IlorDash/HAQuDA/Data/Article/Photos/Assembly_slice.png

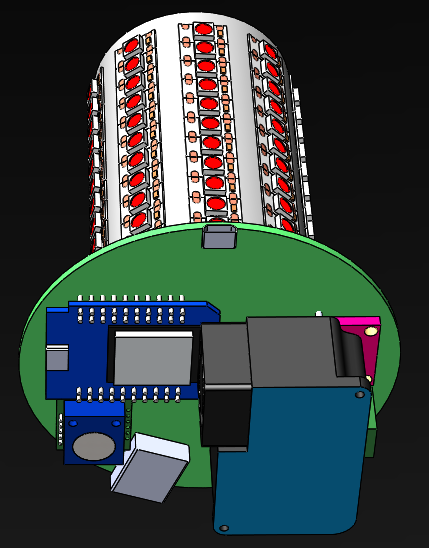
Data/Article/Photos/Assembly_slice.png
