IlorDash/HAQuDA/Data/Article/Photos/Assembly.png

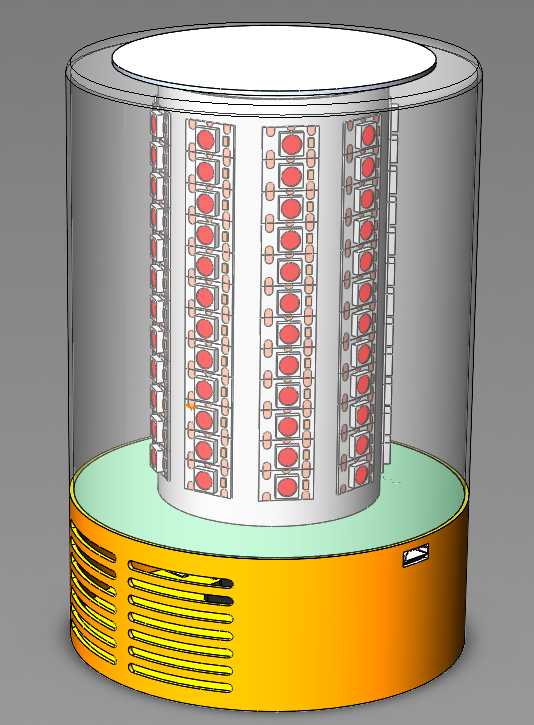
Data/Article/Photos/Assembly.png
