IlorDash/HAQuDA/Data/Article/Photos/AmbientOrb_1.jpg

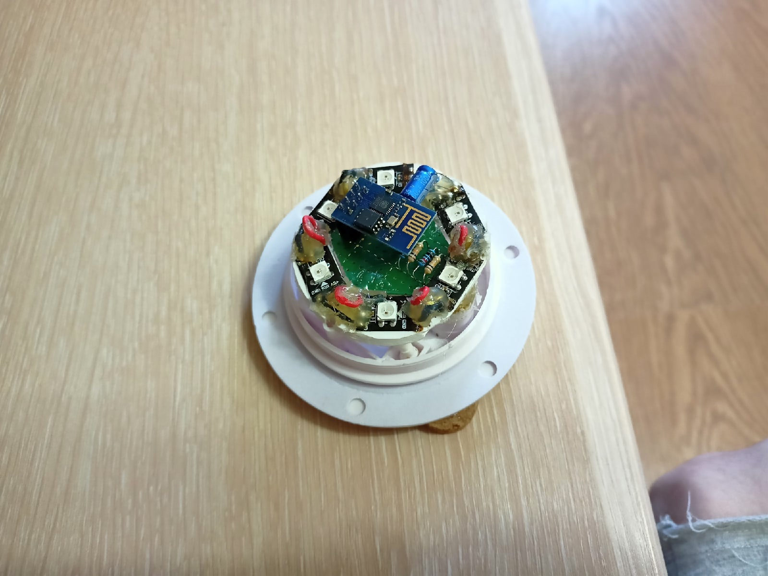
Data/Article/Photos/AmbientOrb_1.jpg
