IlorDash/HAQuDA/Data/Article/Photos/AmbientOrb_DHT_1.jpg

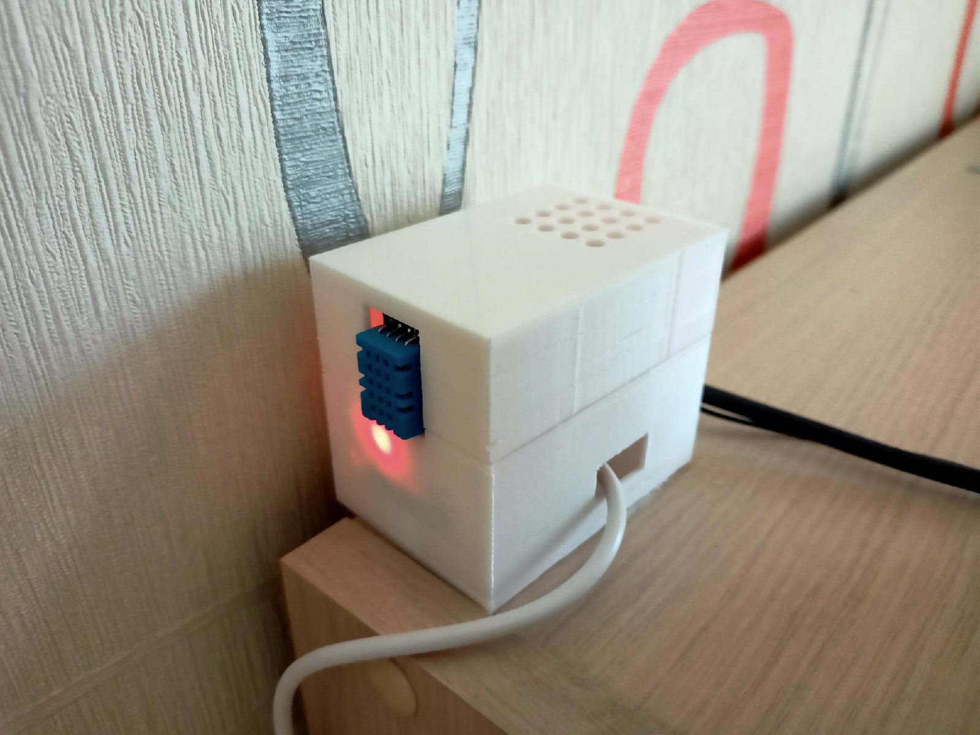
Data/Article/Photos/AmbientOrb_DHT_1.jpg
