IlorDash/HAQuDA/Data/Article/Photos/AmbientOrb_DHT_2.jpg

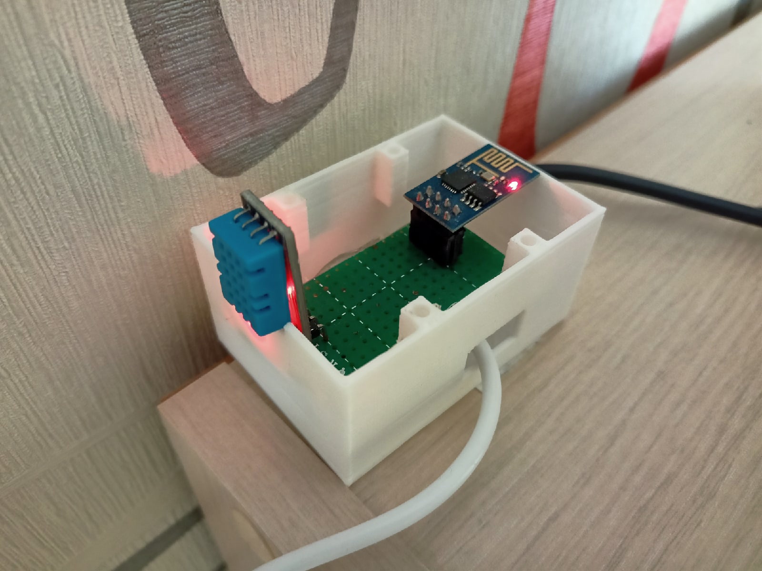
Data/Article/Photos/AmbientOrb_DHT_2.jpg
