IlorDash/HAQuDA/Data/Article/Photos/AmbientOrb_Light.jpg

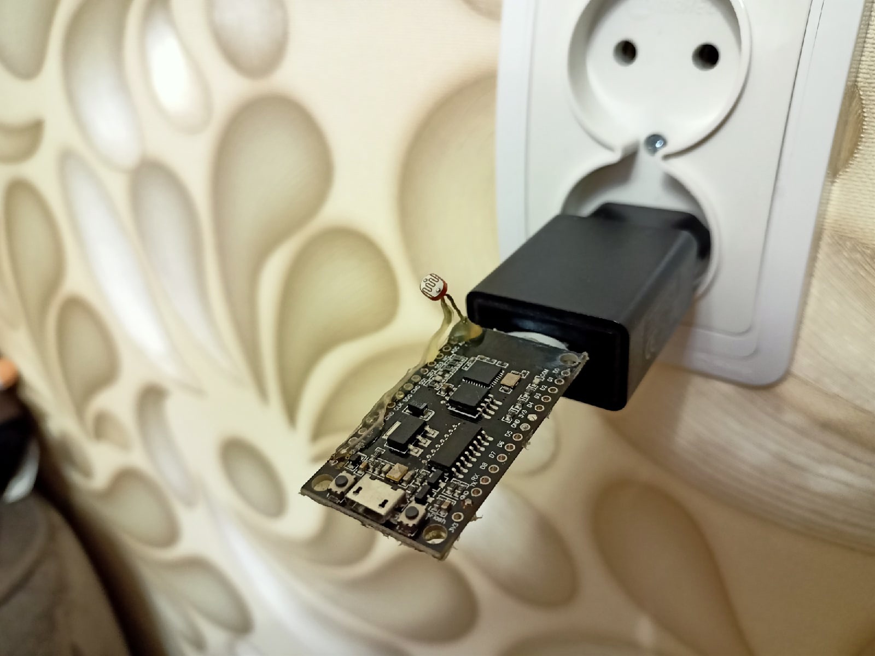
Data/Article/Photos/AmbientOrb_Light.jpg
