IlorDash/HAQuDA/Data/Article/Photos/Multi-mode.png

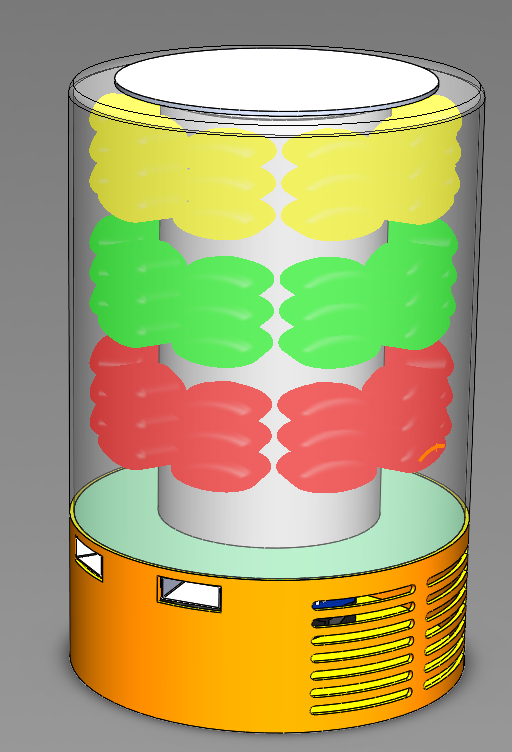
Data/Article/Photos/Multi-mode.png
