IlorDash/HAQuDA/Data/Article/Photos/Night_1.png

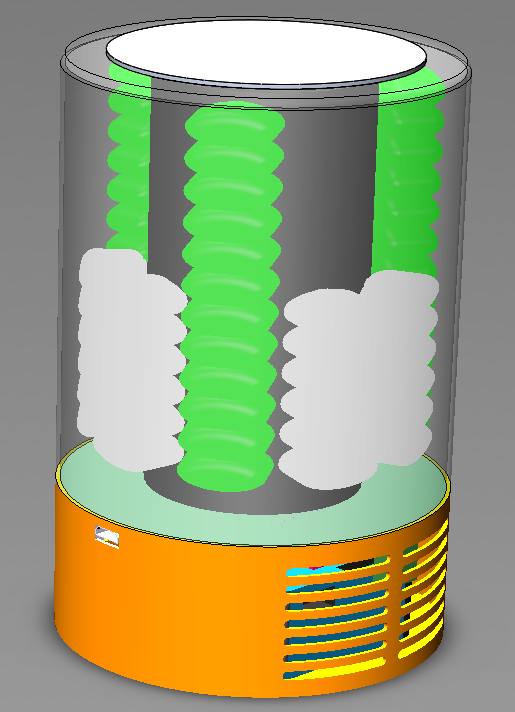
Data/Article/Photos/Night_1.png
