IlorDash/HAQuDA/Data/Article/Photos/Night_2.png

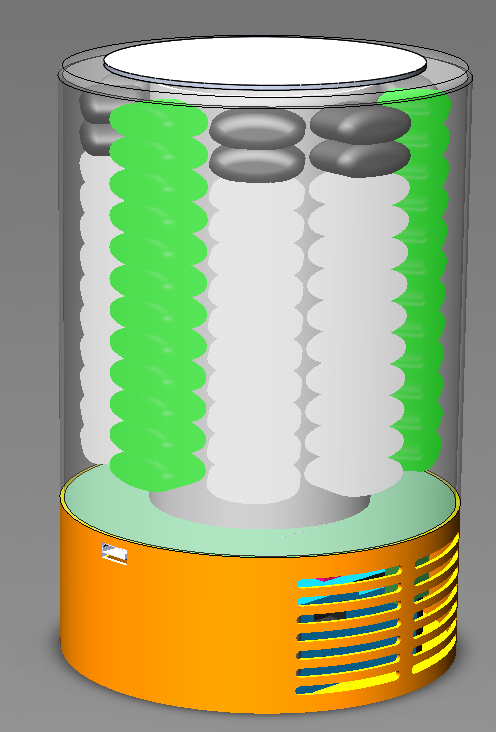
Data/Article/Photos/Night_2.png
