IlorDash/HAQuDA/Data/MCU_Data/MH-ET_LIVE_D1_mini_ESP32_pinout.png

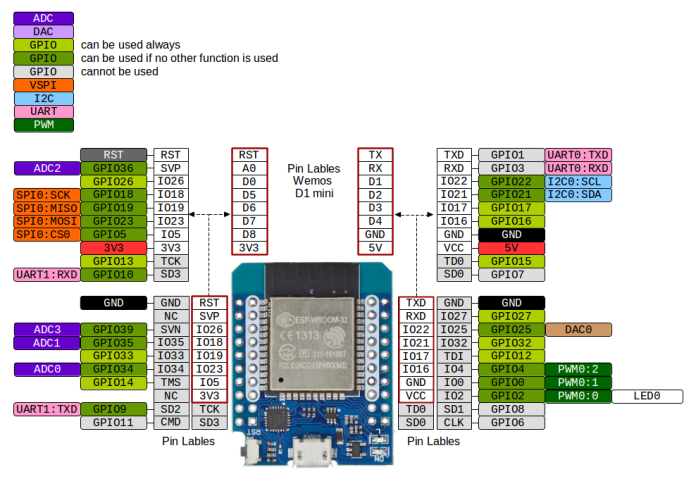
Data/MCU_Data/MH-ET_LIVE_D1_mini_ESP32_pinout.png
