IlorDash/HAQuDA/Models/Body/Lamp_case.SLDPRT

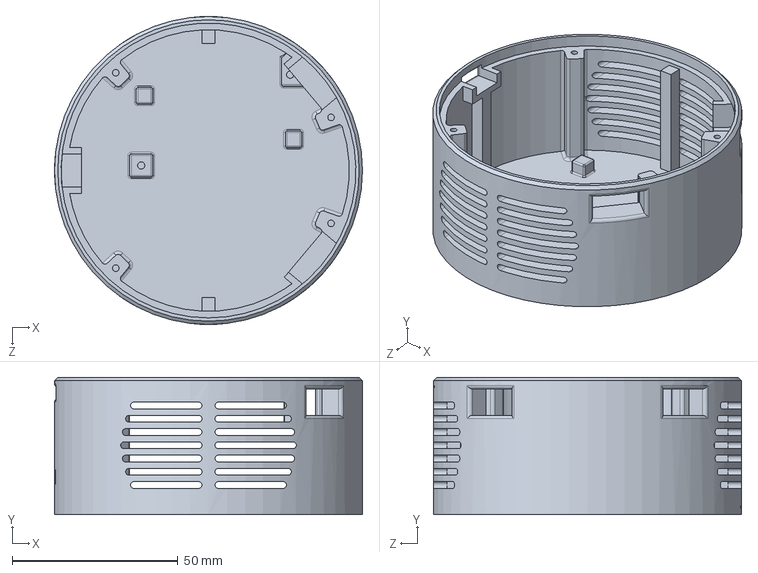
[picture p31: CAD file, 2022-08-22]
Models/Body/Lamp_case.SLDPRT
93.0 x 41.5 x 93.0 mm
