IlorDash/HAQuDA/Models/Details/STEP_files/ESP-32_mini.STEP

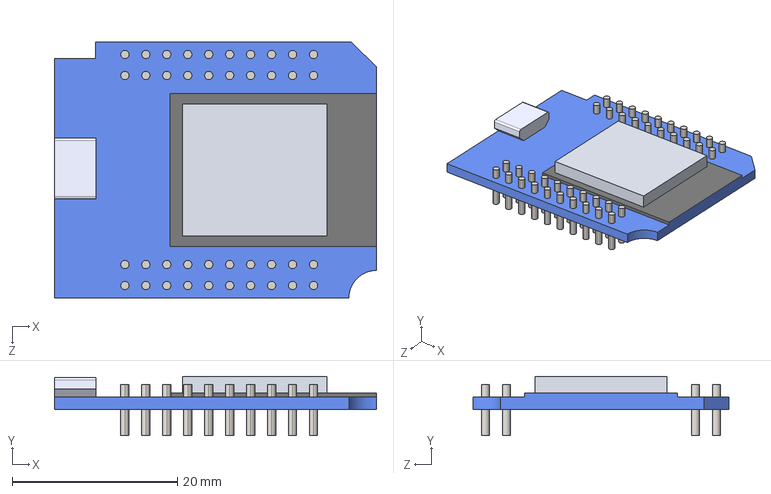
[picture p32: CAD file, 2021-08-23]
Models/Details/STEP_files/ESP-32_mini.STEP
39.0 x 7.20 x 31.0 mm
ESP-32_mini_board^ESP-32_mini_�� 㬮�砭��
USB-Micro_�� 㬮�砭��
