IlorDash/HAQuDA/Models/Body/Diffuser.SLDPRT

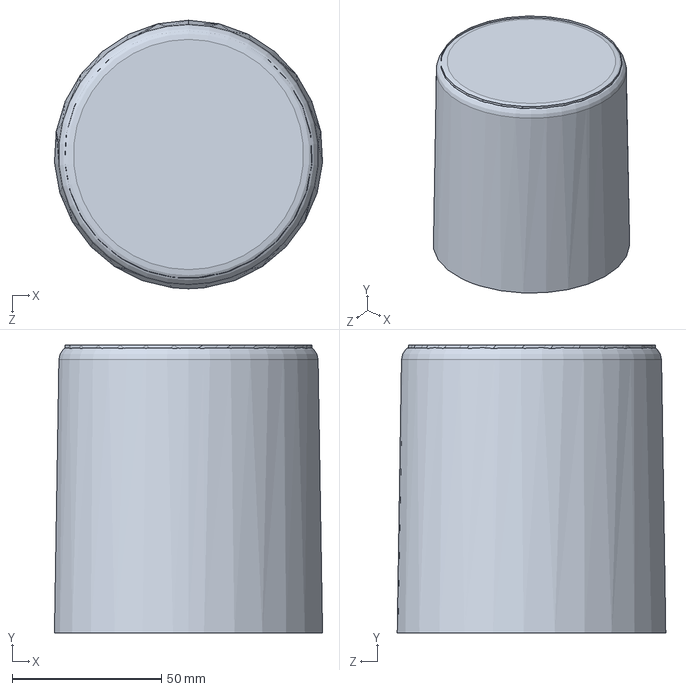
[picture p33: CAD file, 2022-08-22]
Models/Body/Diffuser.SLDPRT
89.8 x 96.5 x 90.0 mm
