IlorDash/HAQuDA/Models/Details/STEP_files/CCS811.STEP

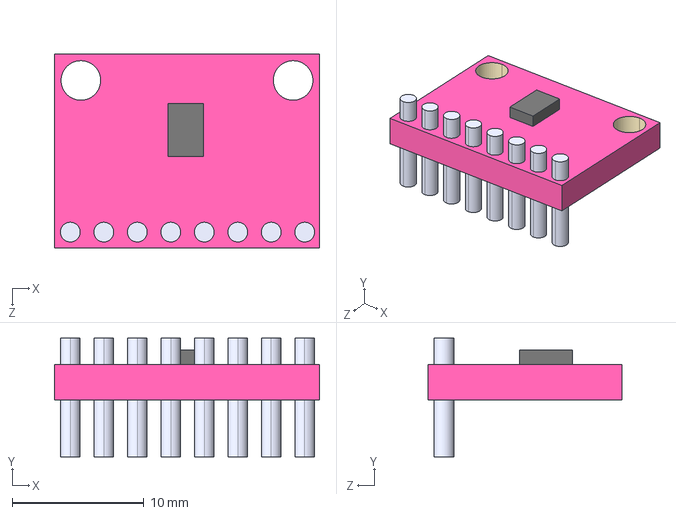
[picture p34: CAD file, 2021-08-23]
Models/Details/STEP_files/CCS811.STEP
20.1 x 9.00 x 14.7 mm
