IlorDash/HAQuDA/Models/Details/ZH03B_DustModule.SLDPRT

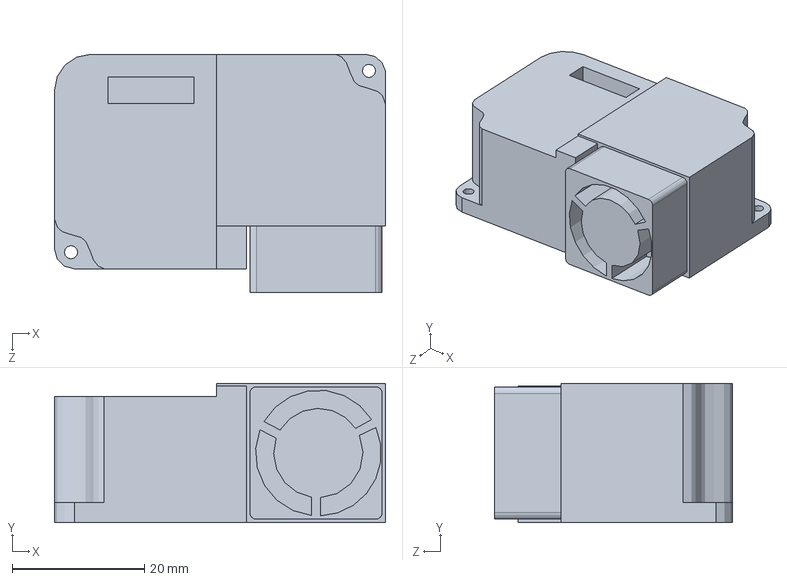
[picture p35: CAD file, 2022-01-29]
Models/Details/ZH03B_DustModule.SLDPRT
50.0 x 21.0 x 36.0 mm
