IlorDash/HAQuDA/Models/Body/Lamp_cap_fastener.SLDPRT

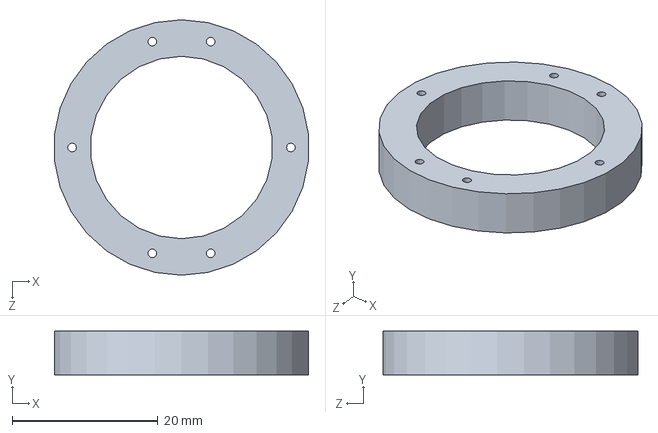
[picture p36: CAD file, 2022-03-07]
Models/Body/Lamp_cap_fastener.SLDPRT
34.8 x 6.00 x 35.0 mm
