IlorDash/HAQuDA/Models/Details/STEP_files/ZE-25-O3_Sensor.STEP

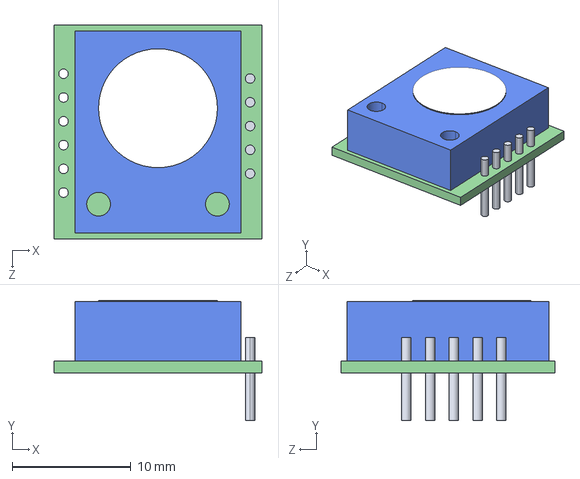
[picture p37: CAD file, 2021-08-23]
Models/Details/STEP_files/ZE-25-O3_Sensor.STEP
17.5 x 10.1 x 18.0 mm
