IlorDash/HAQuDA/Models/Details/WS2812_led.SLDPRT

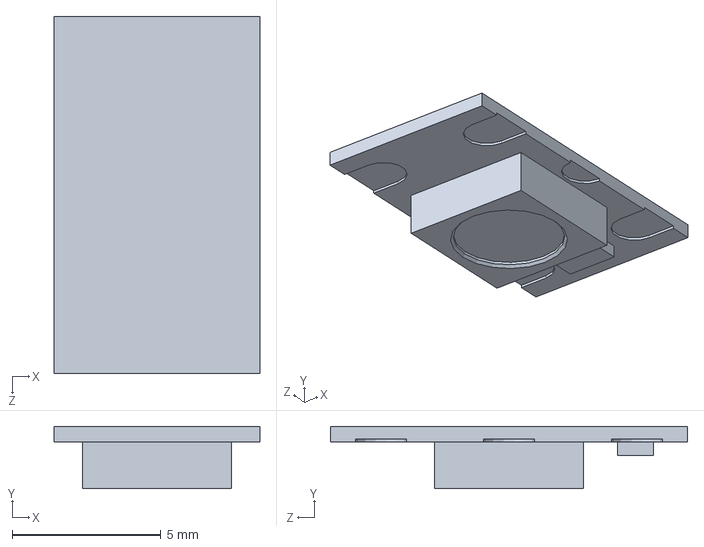
[picture p38: CAD file, 2021-06-08]
Models/Details/WS2812_led.SLDPRT
6.92 x 2.10 x 12.0 mm
