IlorDash/HAQuDA/Models/Details/MP-4_Gas_sensor.SLDPRT

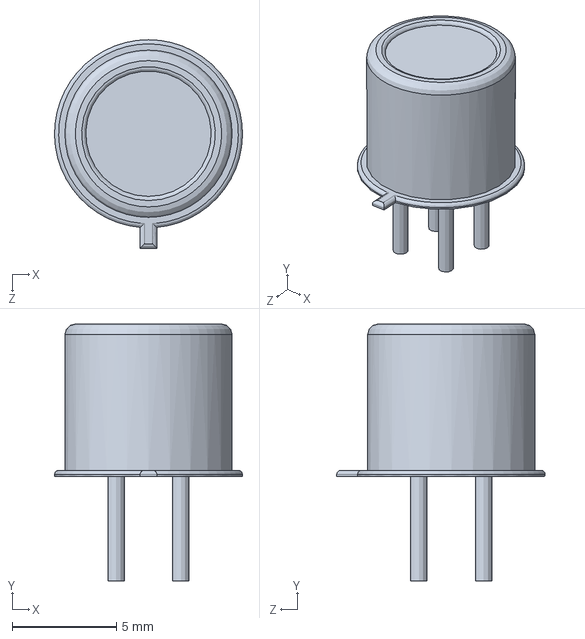
[picture p39: CAD file, 2021-06-08]
Models/Details/MP-4_Gas_sensor.SLDPRT
9.00 x 12.3 x 9.98 mm
