IlorDash/HAQuDA/Models/Details/STEP_files/DHT-11_without_case.STEP

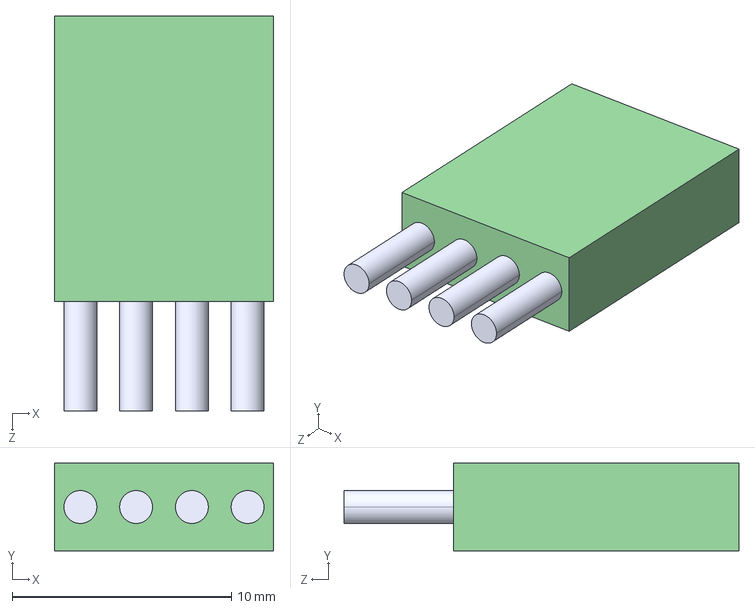
[picture p40: CAD file, 2021-08-23]
Models/Details/STEP_files/DHT-11_without_case.STEP
10.0 x 4.00 x 18.0 mm
