IlorDash/HAQuDA/Models/Demo/DemoLed.SLDPRT

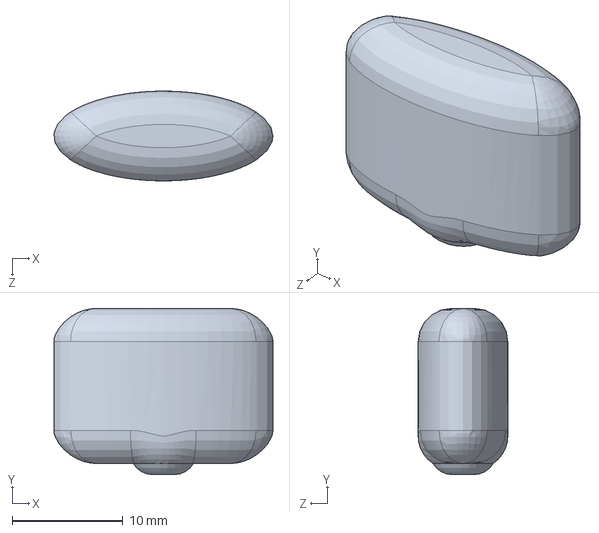
[picture p41: CAD file, 2021-06-08]
Models/Demo/DemoLed.SLDPRT
19.8 x 15.0 x 8.11 mm
